sbcshop/UPS-Hat-RPi/Images/img_1.JPG

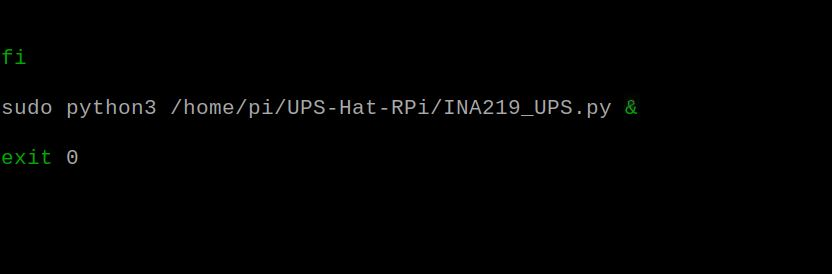
Images/img_1.JPG
